rene-dev/Lasertag/case/1.png

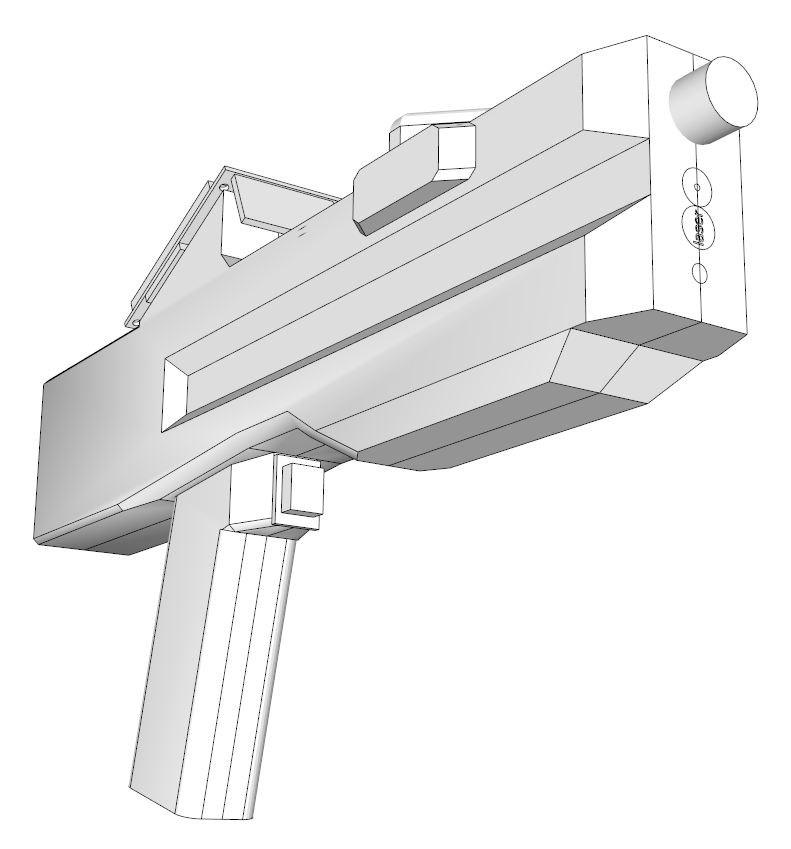
case/1.png
