rene-dev/Lasertag/case/2.png

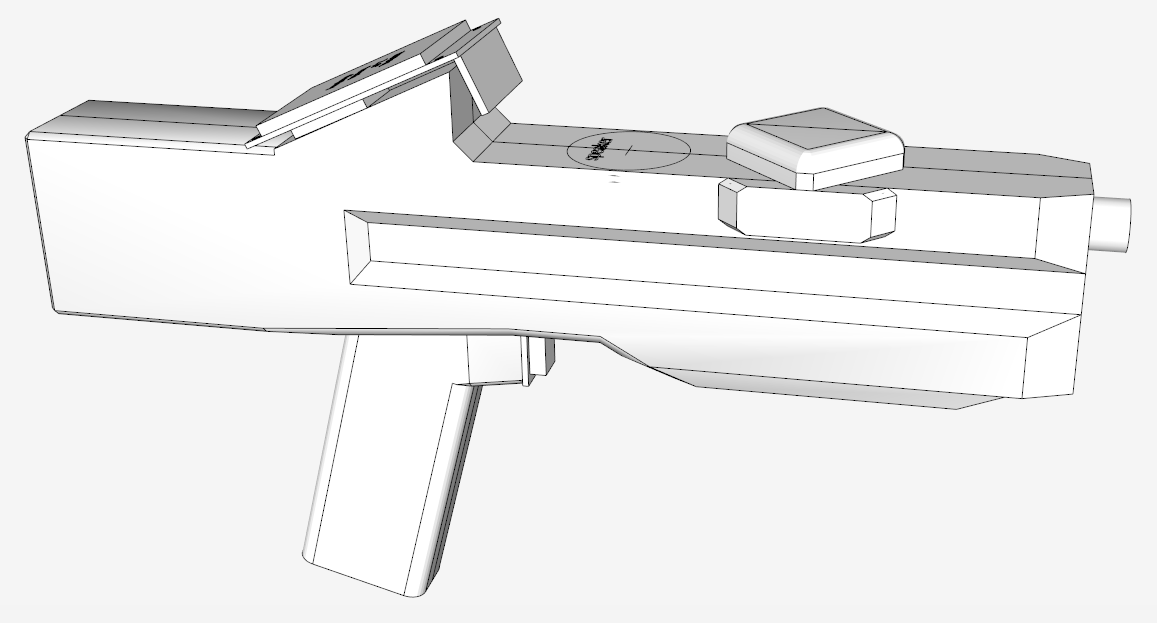
case/2.png
