rene-dev/Lasertag/case/3.png

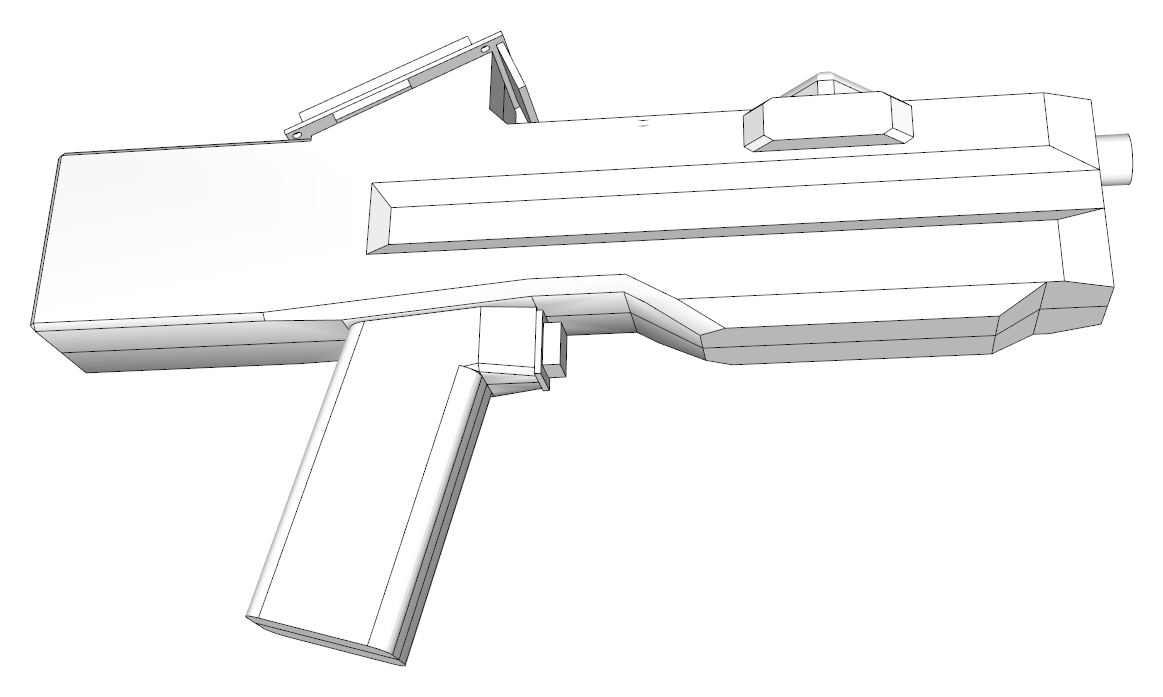
case/3.png
