rene-dev/Lasertag/case/4.png

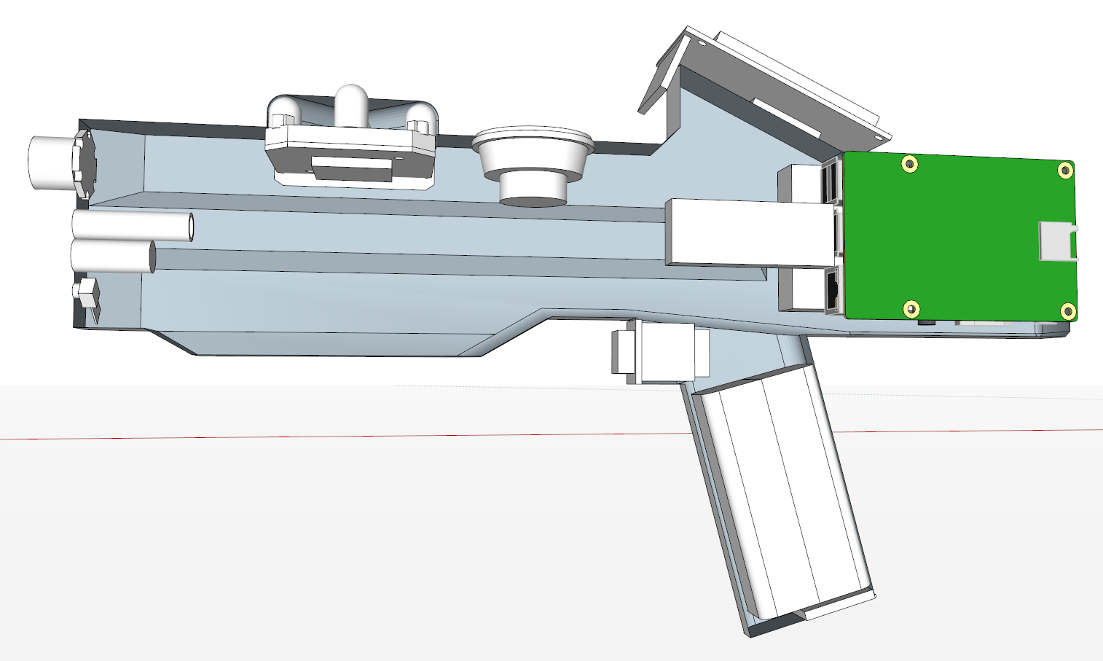
case/4.png
