rene-dev/Lasertag/lasermodule/code/code output test ohne i2c/twislave.c

/*#################################################################################################
	Title	: TWI SLave
	Author	: Martin Junghans <jtronics@gmx.de>
	Hompage	: www.jtronics.de
	Software: AVR-GCC / Programmers Notpad 2
	License	: GNU General Public License 
	
	Aufgabe	:
	Betrieb eines AVRs mit Hardware-TWI-Schnittstelle als Slave. 
	Zu Beginn muss init_twi_slave mit der gewünschten Slave-Adresse als Parameter aufgerufen werden. 
	Der Datenaustausch mit dem Master erfolgt über die Buffer rxbuffer und txbuffer, auf die von Master und Slave zugegriffen werden kann. 
	rxbuffer und txbuffer sind globale Variablen (Array aus uint8_t).
	
	Ablauf:
	Die Ansteuerung des rxbuffers, in den der Master schreiben kann, erfolgt ähnlich wie bei einem normalen I2C-EEPROM.
	Man sendet zunächst die Bufferposition, an die man schreiben will, und dann die Daten. Die Bufferposition wird 
	automatisch hochgezählt, sodass man mehrere Datenbytes hintereinander schreiben kann, ohne jedesmal
	die Bufferadresse zu schreiben.
	Um den txbuffer vom Master aus zu lesen, überträgt man zunächst in einem Schreibzugriff die gewünschte Bufferposition und
	liest dann nach einem repeated start die Daten aus. Die Bufferposition wird automatisch hochgezählt, sodass man mehrere
	Datenbytes hintereinander lesen kann, ohne jedesmal die Bufferposition zu schreiben.
	
	Abgefangene Fehlbedienung durch den Master:
	- Lesen über die Grenze des txbuffers hinaus
	- Schreiben über die Grenzen des rxbuffers hinaus
	- Angabe einer ungültigen Schreib/Lese-Adresse
	- Lesezuggriff, ohne vorher Leseadresse geschrieben zu haben
	
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
//#################################################################################################*/

#include <util/twi.h> 								// Bezeichnungen für Statuscodes in TWSR
#include <avr/interrupt.h> 							// behandlung der Interrupts
#include <stdint.h> 								// definiert Datentyp uint8_t
#include "twislave.h" 								

static volatile uint8_t buffer_adr; 						//"Adressregister" für den Buffer
volatile uint8_t* buffer;
volatile uint8_t buffer_size;



//#################################### Macros
//ACK nach empfangenen Daten senden/ ACK nach gesendeten Daten erwarten
#define TWCR_ACK 	TWCR = (1<<TWEN)|(1<<TWIE)|(1<<TWINT)|(1<<TWEA)|(0<<TWSTA)|(0<<TWSTO)|(0<<TWWC);  

//NACK nach empfangenen Daten senden/ NACK nach gesendeten Daten erwarten     
#define TWCR_NACK 	TWCR = (1<<TWEN)|(1<<TWIE)|(1<<TWINT)|(0<<TWEA)|(0<<TWSTA)|(0<<TWSTO)|(0<<TWWC);

//switched to the non adressed slave mode...
#define TWCR_RESET 	TWCR = (1<<TWEN)|(1<<TWIE)|(1<<TWINT)|(1<<TWEA)|(0<<TWSTA)|(0<<TWSTO)|(0<<TWWC);  

//########################################################################################## init_twi_slave 
void init_twi_slave(uint8_t adr){
	TWAR= adr; //Adresse setzen
	TWCR &= ~(1<<TWSTA)|(1<<TWSTO);
	TWCR|= (1<<TWEA) | (1<<TWEN)|(1<<TWIE);
	buffer = 0;
	sei();
}

//########################################################################################## ISR (TWI_vect) 
//ISR, die bei einem Ereignis auf dem Bus ausgelöst wird. Im Register TWSR befindet sich dann 
//ein Statuscode, anhand dessen die Situation festgestellt werden kann.
ISR (TWI_vect){
	uint8_t data = 0;
	switch (TW_STATUS) 								// TWI-Statusregister prüfen und nötige Aktion bestimmen 
		{
		case TW_SR_SLA_ACK: 						// 0x60 Slave Receiver, wurde adressiert	
			TWCR_ACK; 								// nächstes Datenbyte empfangen, ACK danach
			buffer = 0; 						// Buffer ist undefiniert
			break;

		case TW_SR_DATA_ACK: 						// 0x80 Slave Receiver,Daten empfangen
			data=TWDR; 								// Empfangene Daten auslesen
			if (buffer == 0){ // erster Zugriff
				i2c_slave_poll_buffer(data, &buffer, &buffer_size);
				buffer_adr = 0;
				TWCR_ACK;						// nächstes Datenbyte empfangen, ACK danach, um nächstes Byte anzufordern
			} else {
				buffer[buffer_adr]=data; 		// Daten in Buffer schreiben
				buffer_adr++; 					// Buffer-Adresse weiterzählen für nächsten Schreibzugriff
				if (buffer_adr<(buffer_size-1)){ // im Buffer ist noch Platz für mehr als ein Byte
					TWCR_ACK;				// nächstes Datenbyte empfangen, ACK danach, um nächstes Byte anzufordern
				} else {
					TWCR_NACK;				// letztes Byte lesen, dann NACK, um vollen Buffer zu signaliseren
				}
			}
			break;

		case TW_ST_SLA_ACK: 						//
		case TW_ST_DATA_ACK: 						// 0xB8 Slave Transmitter, weitere Daten wurden angefordert
			
			if (buffer){
				TWDR = buffer[buffer_adr]; 			// Datenbyte senden 
				buffer_adr++; 							// bufferadresse für nächstes Byte weiterzählen
			} else {
				TWDR = 0; 					// zuvor keine Leseadresse angegeben! 	
			}
			
			if (buffer_adr < (buffer_size-1)){				// im Buffer ist mehr als ein Byte, das gesendet werden kann
				TWCR_ACK; 						// nächstes Byte senden, danach ACK erwarten
			} else {
				TWCR_NACK; 						// letztes Byte senden, danach NACK erwarten
			}
			break;

		case TW_ST_DATA_NACK: 						// 0xC0 Keine Daten mehr gefordert 
		case TW_ST_LAST_DATA: 						// 0xC8  Last data byte in TWDR has been transmitted (TWEA = “0”); ACK has been received
			i2c_slave_read_complete();
			TWCR_RESET; 							// Übertragung beenden, warten bis zur nächsten Adressierung
			break;
			
		case TW_SR_DATA_NACK: 						// 0x88 
		case TW_SR_STOP: 						// 0xA0 STOP empfangen
			i2c_slave_write_complete();
			TWCR_RESET; 							// Übertragung beenden, warten bis zur nächsten Adressierung
			break;
			
		default:
			TWCR_RESET; 							// Übertragung beenden, warten bis zur nächsten Adressierung
			break;
	} //end.switch (TW_STATUS)
} //end.ISR(TWI_vect)
